mubes/garonne/m4/App/config.c

/*
*                                       ++++++++++++++++++
*                                  +++++++++++++++++++++++++++++
*                              +++++++                      +++++++++
*                          +++++++                               +++++++++++++
*         ++++++++++++++++++++                                         ++++++++++
*    +++++++++++++++++++++                                                     +++
*   +++++                                                                       +++
*  +++         ######### ######### ########  #########  #########   +++++++      ++
*  +++  +++++ ####  #### ######## ####  #### ##### #### #### ####  +++  ++++    +++
*  +++   ++++ ###     ## ###      ###    ### ###    ### ###    ### ++++++++   +++
*   ++++ ++++ ########## ###      ########## ###    ### ###    ### ++++    +++++
*    +++++++   ###### ## ###       ########  ###     ## ##     ###  ++++++++++
*
* Copyright 2017 Technolution BV  opensource@technolution.eu
*
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
* Config Store and Restore
* ========================
*
* Available everywhere, this is the configuration management module that stores and loads configuration parameters.
* The actual structure of the config is opaque, and known only in this module. Accessors are provided to get to/from
* parameters.
*
*/

#include <string.h>
#include <stdarg.h>
#include <stdio.h>
#include <ctype.h>
#include <stdlib.h>
#include "config.h"
#include "serport.h"
#include "gio.h"
#include "eeprom.h"

#define ID_BASE     (0x40045000)
#define EEPROM_BASE (0x20040000)

#define ITM_CONSOLE                     /* Send debug output to ITM Channel (or Terminal, otherwise) */

ConfigType ConfigStore __attribute__( ( section ( ".m0m4" ) ) ); /* Current configuration (may not be the same as the saved version! */
ConfigType *ConfigStorePtr = &ConfigStore;  /* Pointer to the configuration store */
BOOL wasDefaulted;                      /* Indication of if this load was a defaulting load */
BOOL isSaved;                           /* Indication of if the current configuration has been saved */
static uint32_t chipSerialNumber[4];    /* Storage for chip serial number */

// ============================================================================================
// Structure of the EEPROM storage - This is internal!!
// ===============================


#define EEPROM_CONFIG_OFFSET (0)    // Location of config in EEPROM


// ============================================================================================
// ============================================================================================
// ============================================================================================
// Publicly available routines
// ============================================================================================
// ============================================================================================
// ============================================================================================
void ConfigAssertDA( char *msg, char *file, uint32_t line )

/* This is a locking Assert loop (print error message and lockup tigher than a Ducks A...) */
{

    uint32_t spin = 1;
    uint32_t activeLed = 0;
    uint32_t nopCount = 0;

    while ( spin )
    {
        vTaskSuspendAll(); /* We don't want tasks running while this is going on */
        __disable_irq();
        dbgprint( "%s: %s line %d" EOL, ( msg == NULL ) ? "Assert Fail" : msg, file, line );

        /* Cycle the LEDs to give a visual indication of the assert */
        /* This is a waste of battery, but at least it's only under exception conditions */
        GIOdebugLedToggle( activeLed );
        nopCount = 1000000;

        while ( nopCount-- )
        {
            __asm__( "NOP" );
        }

        GIOdebugLedToggle( ( activeLed + 1 ) % NUM_DEBUG_LEDS );
        activeLed = ( activeLed + 1 ) % NUM_DEBUG_LEDS;
        nopCount = 1000000;

        while ( nopCount-- )
        {
            __asm__( "NOP" );
        }
    }

    __enable_irq();
    xTaskResumeAll();
}
// ============================================================================================

#ifdef ITM_CONSOLE
void dbgprint( char *fmt, ... )

{
    static char op[80];
    char *p = op;

    va_list va;
    va_start( va, fmt );
    vsiprintf( op, fmt, va );
    va_end( va );

    while ( *p != '\0' )
    {
        /* Filter DOS line endings */
        if ( ( *p == '\n' && *( p + 1 ) == '\r' ) || ( *p == '\r' && *( p + 1 ) == '\n' ) )
        {
            ITM_SendChar( '\n' );
            p += 2;
        }
        else
        {
            ITM_SendChar( *p++ );
        }
    }
}
#else
#ifdef DEBUG_ON_TERMINAL
void dbgprint( char *fmt, ... )

{
    static char op[PRINTF_MAXLEN];

    va_list va;
    va_start( va, fmt );
    vsiprintf( op, fmt, va );
    va_end( va );
    ASSERT( strlen( op ) <= PRINTF_MAXLEN );
    uartTx( TERMINAL_PORT, ( uint8_t * ) op, strlen( op ) );
}
#else
void dbgprint( char *fmt, ... )

{
}
#endif
#endif
// ============================================================================================
static void _EEPROM_Read( uint32_t ofs, void *d, uint32_t count )

{
    ofs += EEPROM_BASE;

    /* Do full 32-bit transfers as far as possible */
    while ( count > 3 )
    {
        *( uint32_t * )d = *( ( uint32_t * )ofs );
        ofs += 4;
        d += 4;
        count -= 4;
    }

    /* Deal with any residual bytes */
    uint8_t *db = ( uint8_t * )d;

    while ( count-- )
    {
        *db++ = *( ( uint8_t * )ofs++ );
    }
}
// ============================================================================================
static void _EEPROM_Write( uint32_t ofs, uint32_t *ptr, uint32_t size )

{
    ofs += EEPROM_BASE;

    while ( size )
    {
        *( ( uint32_t * )ofs ) = *ptr++;
        ofs += 4;
        size = ( size > 4 ) ? size - 4 : 0;

        if ( ( !size ) || ( !( ofs & 0x7f ) ) )
        {
            Chip_EEPROM_EraseProgramPage( LPC_EEPROM );
        }
    }
}
// ============================================================================================
// ============================================================================================
// ============================================================================================
// Publicly available routines
// ============================================================================================
// ============================================================================================
// ============================================================================================
void ConfigInit( void )

/* Initialise a configuration either from EEPROM or default if EEPROM isn't valid */

{
    uint32_t magicCheck;
    uint32_t readLength;

    /* First things first, identify the chip */
    /* read serial - stored in magic location ... See UM10503 Rev 1.9 Pg 42 (Table 14) */
    for ( uint32_t i = 0; i < 4; i++ )
    {
        chipSerialNumber[i] = ( ( uint32_t * )ID_BASE )[i];
    }

    Chip_EEPROM_Init( LPC_EEPROM );
    Chip_EEPROM_SetAutoProg( LPC_EEPROM, EEPROM_AUTOPROG_OFF );


    ConfigStore = ( ConfigType )DEFAULT_CONFIG;
    wasDefaulted = TRUE;
    isSaved = FALSE;

    _EEPROM_Read( EEPROM_CONFIG_OFFSET, &magicCheck, sizeof( uint32_t ) );

    if ( MAGICNUMBER == magicCheck )
    {
        /* There's something useful here, overload it onto the pre-config */
        _EEPROM_Read( EEPROM_CONFIG_OFFSET + sizeof( uint32_t ), &readLength, sizeof( uint32_t ) );

        if ( readLength <= sizeof( ConfigStore ) )
        {
            /* Only read it in if its a sane length */
            _EEPROM_Read( EEPROM_CONFIG_OFFSET + 2 * sizeof( uint32_t ), &ConfigStore, readLength );
            wasDefaulted = FALSE;
            isSaved = TRUE;
        }
    }
}
// ============================================================================================
const uint32_t *ConfigGetSerialNumber( void )

/* Return serial number of the chip */

{
    return chipSerialNumber;
}
// ============================================================================================
BOOL ConfigCommit( void )

/* Save the current configuration to EEPROM */

{
    uint32_t scratch = MAGICNUMBER;

    _EEPROM_Write( EEPROM_CONFIG_OFFSET, &scratch, sizeof( uint32_t ) );
    scratch = sizeof( ConfigStore );
    _EEPROM_Write( EEPROM_CONFIG_OFFSET + sizeof( uint32_t ), &scratch, sizeof( uint32_t ) );
    _EEPROM_Write( EEPROM_CONFIG_OFFSET + 2 * sizeof( uint32_t ), ( uint32_t * )&ConfigStore, sizeof( ConfigStore ) );

    isSaved = TRUE;
    wasDefaulted = FALSE;
    return TRUE;
}
// ============================================================================================
