mubes/garonne/m4/App/speedy.c

#ifndef INC_AUDIO_SAMPLES_H_
#define INC_AUDIO_SAMPLES_H_
#include "config.h"
const uint32_t speedy[] =
{
    0x18000, 0x18000, 0x18000, 0x18000,
    0x18000, 0x18000, 0x18000, 0x18000,
    0x18000, 0x18000, 0x18000, 0x18000,
    0x18000, 0x18000, 0x18000, 0x18000,
    0x18000, 0x18000, 0x18000, 0x18000,
    0x18000, 0x18000, 0x18000, 0x18000,
    0x18000, 0x18000, 0x18000, 0x18000,
    0x18000, 0x18000, 0x18000, 0x18000,
    0x17F00, 0x17F00, 0x17F00, 0x17E00,
    0x17E00, 0x17E00, 0x17F00, 0x17F00,
    0x17F00, 0x18000, 0x18000, 0x18000,
    0x18000, 0x18000, 0x17F00, 0x17E00,
    0x17C00, 0x17C00, 0x17E00, 0x18000,
    0x18000, 0x18000, 0x18000, 0x18000,
    0x18000, 0x18000, 0x18000, 0x18000,
    0x18100, 0x18200, 0x18100, 0x18100,
    0x18000, 0x17E00, 0x17E00, 0x17E00,
    0x17F00, 0x17F00, 0x18000, 0x18100,
    0x18100, 0x18000, 0x17F00, 0x18000,
    0x18000, 0x18100, 0x18100, 0x18200,
    0x18400, 0x18200, 0x18200, 0x18100,
    0x18000, 0x17E00, 0x17C00, 0x17E00,
    0x18000, 0x18200, 0x18200, 0x18100,
    0x18100, 0x18100, 0x18100, 0x18200,
    0x18400, 0x18800, 0x18B00, 0x18B00,
    0x18B00, 0x18800, 0x18200, 0x17F00,
    0x17C00, 0x17C00, 0x17800, 0x17500,
    0x17700, 0x17800, 0x17A00, 0x17A00,
    0x17B00, 0x17F00, 0x18000, 0x18000,
    0x17E00, 0x17F00, 0x18000, 0x17E00,
    0x17C00, 0x17B00, 0x17800, 0x17300,
    0x17000, 0x17400, 0x17C00, 0x18000,
    0x18000, 0x18100, 0x18200, 0x18200,
    0x18400, 0x18500, 0x18800, 0x18B00,
    0x18800, 0x18600, 0x18400, 0x17E00,
    0x17500, 0x17000, 0x17000, 0x17100,
    0x17000, 0x17100, 0x17500, 0x17500,
    0x17400, 0x17300, 0x17000, 0x17700,
    0x17A00, 0x17500, 0x17B00, 0x17C00,
    0x17B00, 0x17F00, 0x17E00, 0x17E00,
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
};
#endif
